thechakmv/Overdrive-Distortion-Guitar-Pedal/ltspice/Overdrive_Distortion_Schematic.asc

C1: cap; 100nF
C2: cap; 47nF
C3: cap; 51pF
C4: cap; 100nF
C5: cap; 470pF
C6: cap; 47µ
C7: cap; 100n
C8: cap; 10n
C9: cap; 10n
C10: cap; 20n
C11: cap; 22n
C12: cap; 100nF
C13: cap; 1µ
C14: cap; 100nF
C15: cap; 100µF
Cin: cap; 100nF
D1: diode; 1N4148
D2: diode; 1N4148
D3: diode; 1N4148
D4: diode; 1N4148
Pot1: res; 500K
R1: res; 1Meg
R2: res; 1Meg
R3: res; 51K
R4: res; 4.7K
R5: res; 470
R6: res; 1Meg
R7: res; 500K
R8: res; 1K
R9: res; 20K
R10: res; 1Meg
R11: res; 1Meg
R12: res; 20K
R13: res; 10K
R14: res; 10K
R15: res; 0
R16: res; 0
R17: res; 1K
R18: res; 100K
R19: res; 1Meg
R20: res; 1Meg
R21: res; 470
Rout: res; 470
Rpull]: res; 1Meg
U1: OP07
U2: OP07
U3: OP07
U4: OP07
V1: signal; AC 1
V2: voltage; 9V
Named nets: 0, Vpow, Vref, Vs, Vin, Vod, Vtt, Vds, Vtc, Vout
Overdrive Stage
Distortion Stage
Tone/Volume Control
.ac dec 100 10 20K
