thechakmv/Overdrive-Distortion-Guitar-Pedal/ltspice/Overdrive.asc

C1: cap; 47nF
C2: cap; 51pF
C3: cap; 100nF
D1: diode; 1N4148
D2: diode; 1N4148
Pot1: res; 500K
R1: res; 4.7K
R2: res; 51K
R3: res; 470
R4: res; 1Meg
R5: res; 1Meg
U1: OP07
V1: voltage; 9V
V2: signal; AC 1
Named nets: Vpow, 0, Vref, Vout, Vin, Vs
Overdrive Stage
.ac dec 100 10 20K
